drgerg/Pi-based-weather-station/Pics/BME280_mount-for-chimney.jpg

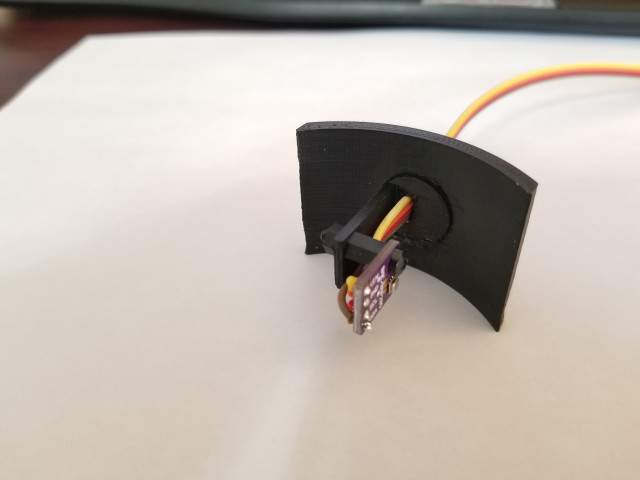
Pics/BME280_mount-for-chimney.jpg
