drgerg/Pi-based-weather-station/Pics/bottom-mount-hinge-perspective-view.jpg

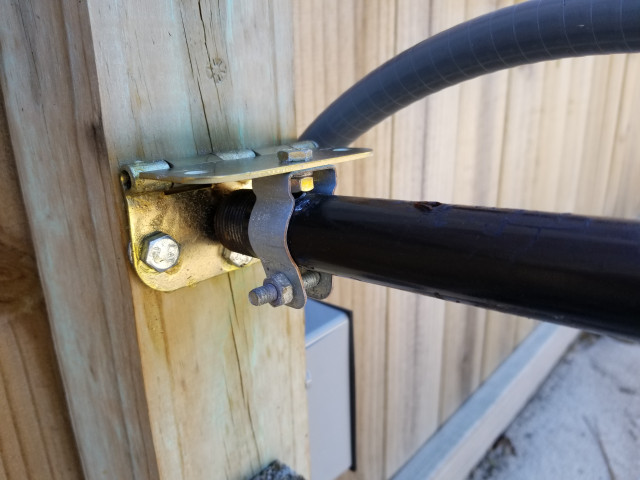
Pics/bottom-mount-hinge-perspective-view.jpg
