drgerg/Pi-based-weather-station/Pics/box-for-12VDC-arrestor-at-pole.jpg

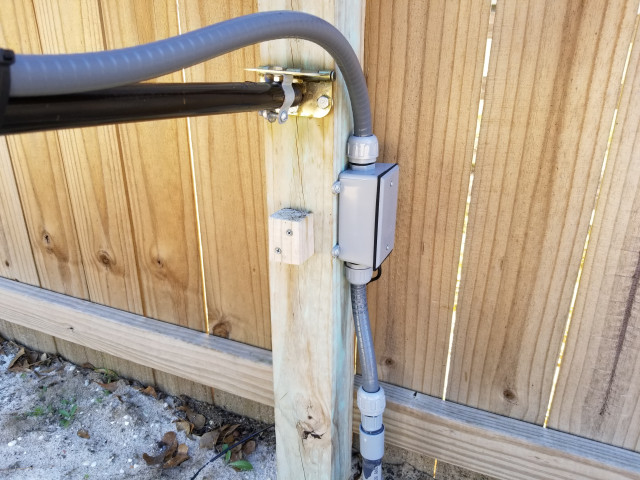
Pics/box-for-12VDC-arrestor-at-pole.jpg
