drgerg/Pi-based-weather-station/Pics/camera-module.jpg

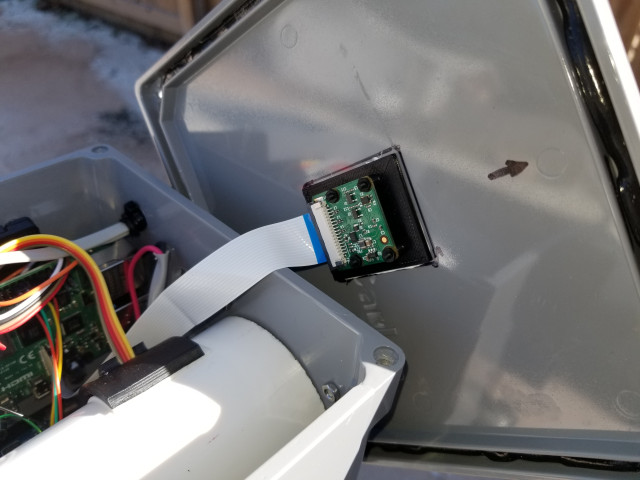
Pics/camera-module.jpg
