drgerg/Pi-based-weather-station/Pics/custom-10-pin-header.jpg

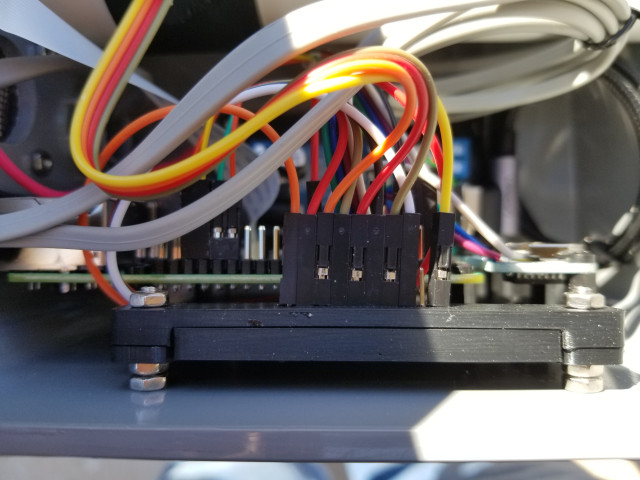
Pics/custom-10-pin-header.jpg
