drgerg/Pi-based-weather-station/Pics/DROK-buck-DC2DC-converter.jpg

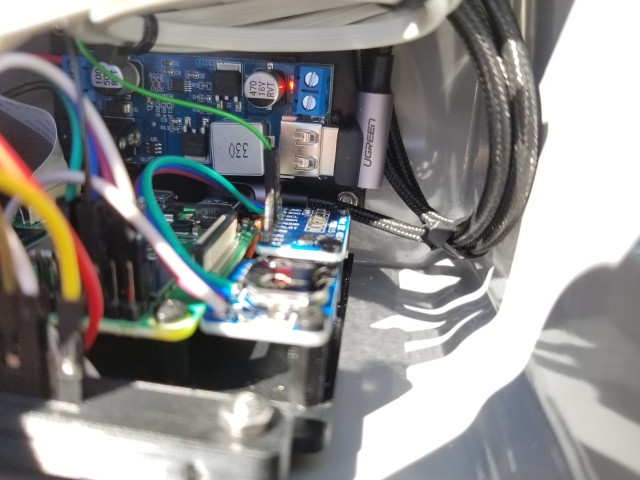
Pics/DROK-buck-DC2DC-converter.jpg
