drgerg/Pi-based-weather-station/Pics/Everything-guts-out-full-size.jpg

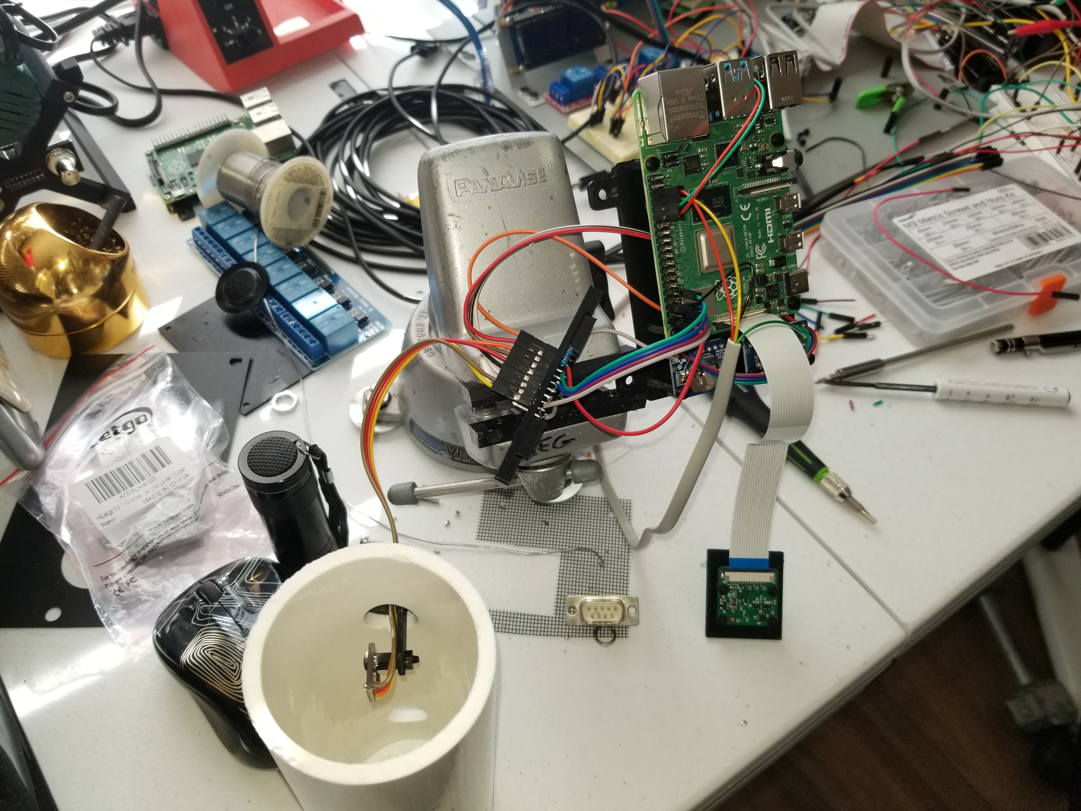
Pics/Everything-guts-out-full-size.jpg
