drgerg/Pi-based-weather-station/Pics/Inside-the-box.jpg

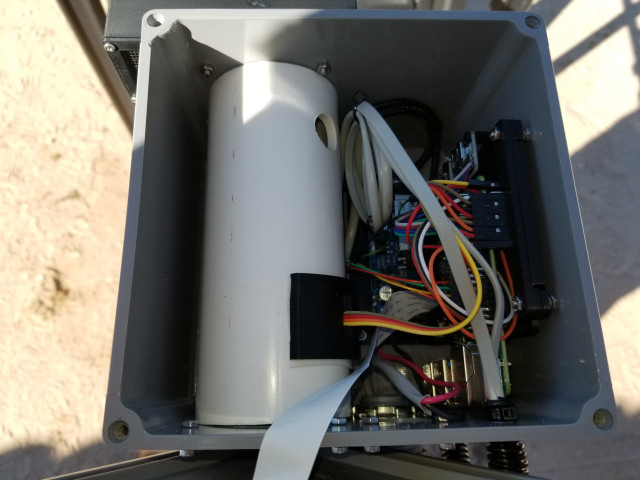
Pics/Inside-the-box.jpg
