drgerg/Pi-based-weather-station/Pics/module-mounting-nylon-standoffs.jpg

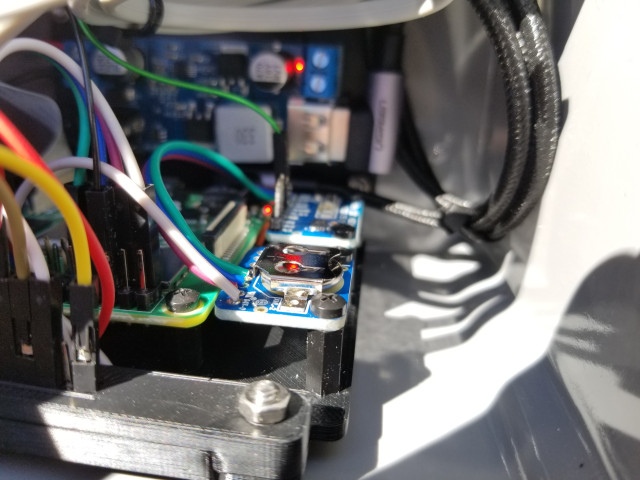
Pics/module-mounting-nylon-standoffs.jpg
