drgerg/Pi-based-weather-station/Pics/mother_main_screen.png

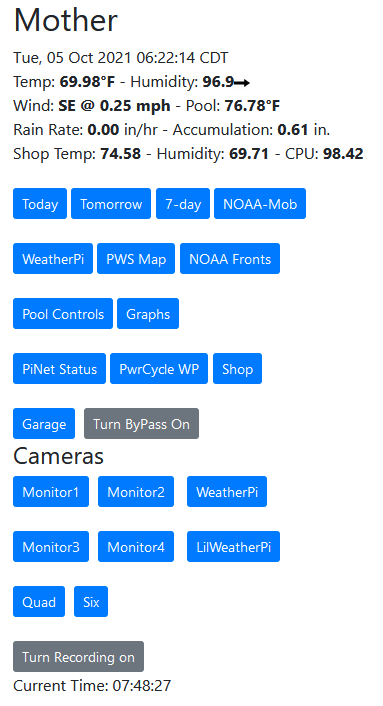
Pics/mother_main_screen.png
