drgerg/Pi-based-weather-station/Pics/outdata.outraw_table.jpg

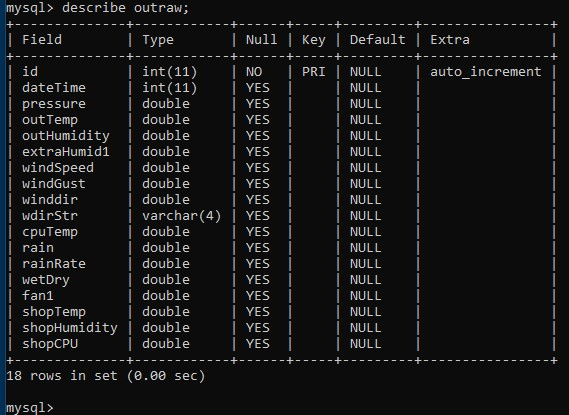
Pics/outdata.outraw_table.jpg
