drgerg/Pi-based-weather-station/Pics/Pi-mount-ADC-RTC.jpg

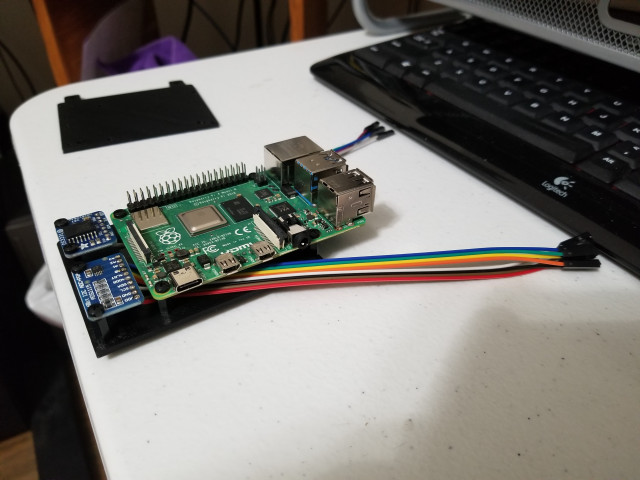
Pics/Pi-mount-ADC-RTC.jpg
