drgerg/Pi-based-weather-station/Pics/Screen_lookingUpChimney.jpg

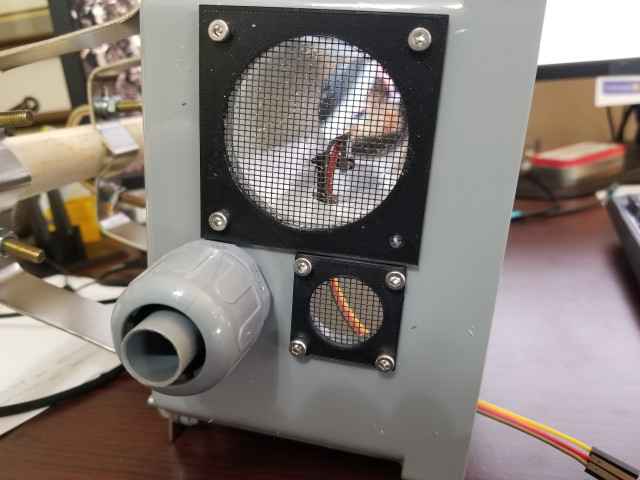
Pics/Screen_lookingUpChimney.jpg
