drgerg/Pi-based-weather-station/Pics/sensor-wires-enter-pipe.jpg

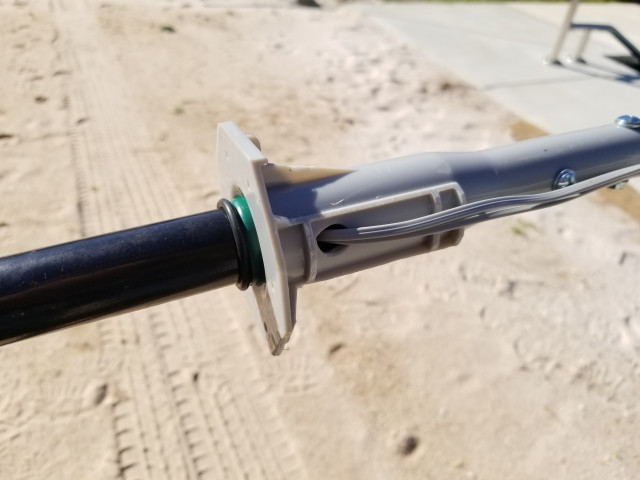
Pics/sensor-wires-enter-pipe.jpg
