drgerg/Pi-based-weather-station/Component_Docs/Power Parts/120VAC to 12VDC power supply.jpg

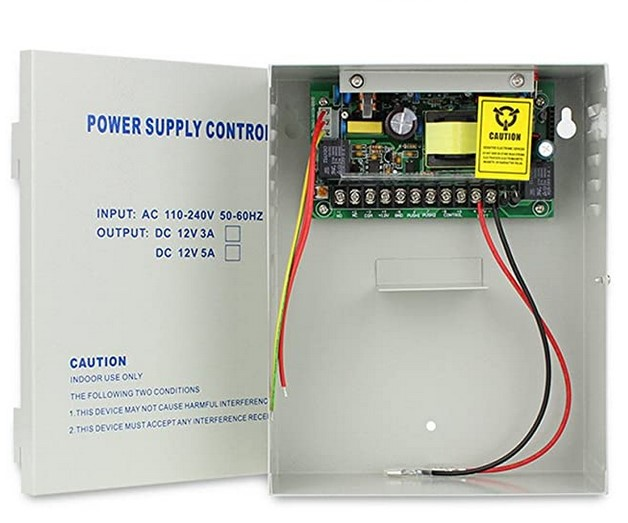
Component_Docs/Power Parts/120VAC to 12VDC power supply.jpg
