drgerg/Pi-based-weather-station/Component_Docs/Power Parts/DROK USB Buck Converter Voltage Regulator.png

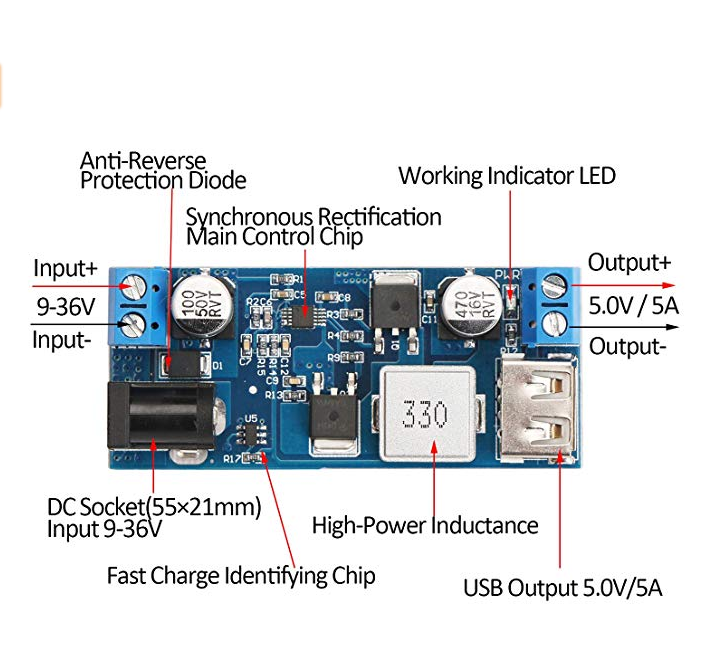
Component_Docs/Power Parts/DROK USB Buck Converter Voltage Regulator.png
