drgerg/Pi-based-weather-station/Component_Docs/Power Parts/LRS01-DC12V Lightning Arrestor.jpg

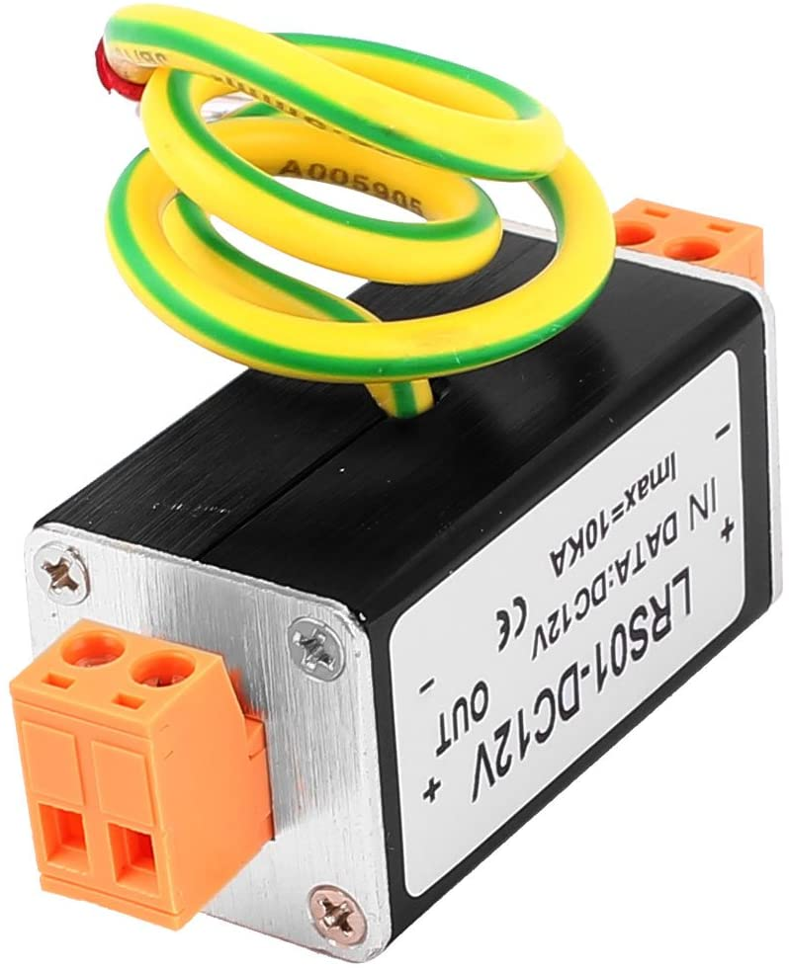
Component_Docs/Power Parts/LRS01-DC12V Lightning Arrestor.jpg
