drgerg/Pi-based-weather-station/Component_Docs/Power Parts/Weatherproof box for Power Supply.jpg

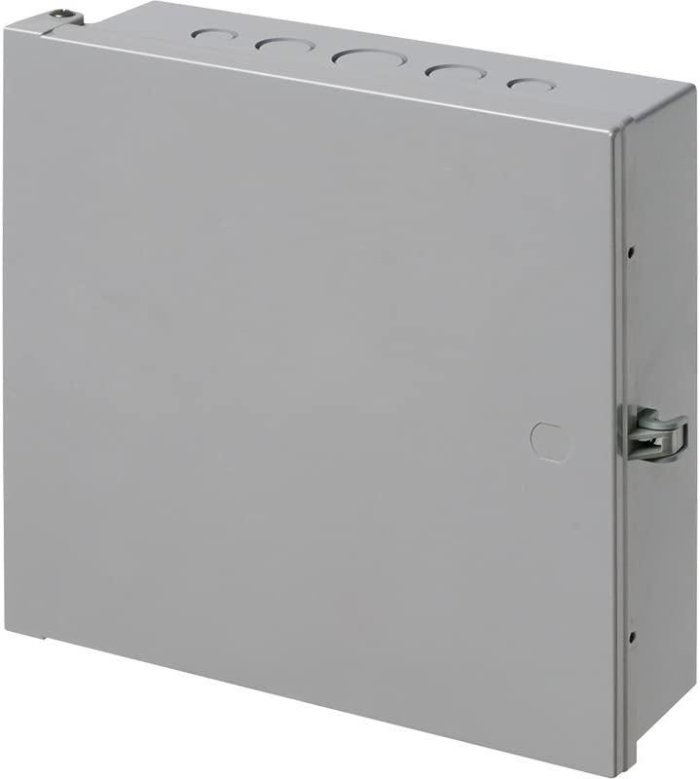
Component_Docs/Power Parts/Weatherproof box for Power Supply.jpg
