drgerg/Pi-based-weather-station/Pics/another-view-of-components.jpg

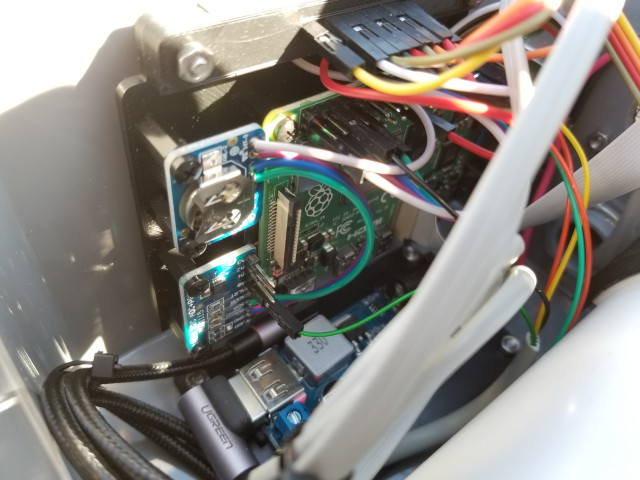
Pics/another-view-of-components.jpg
