drgerg/Pi-based-weather-station/Component_Docs/Fan_Ventilation_Custom/4-wireVariableSpeedFanWiringBeginningPoint.jpg

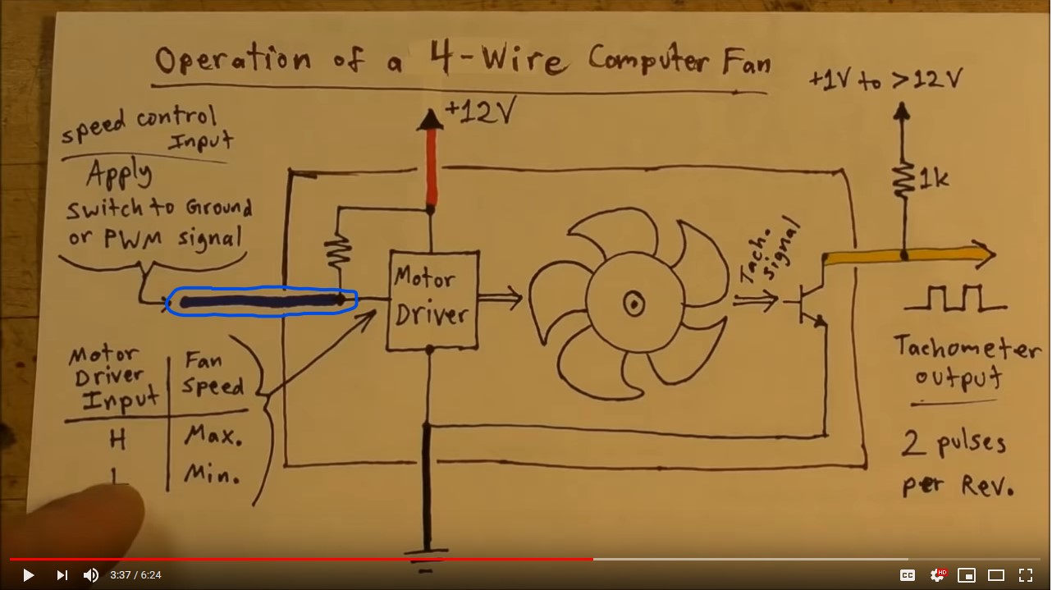
Component_Docs/Fan_Ventilation_Custom/4-wireVariableSpeedFanWiringBeginningPoint.jpg
