drgerg/Pi-based-weather-station/Component_Docs/Power Parts/Completed power supply installed.jpg

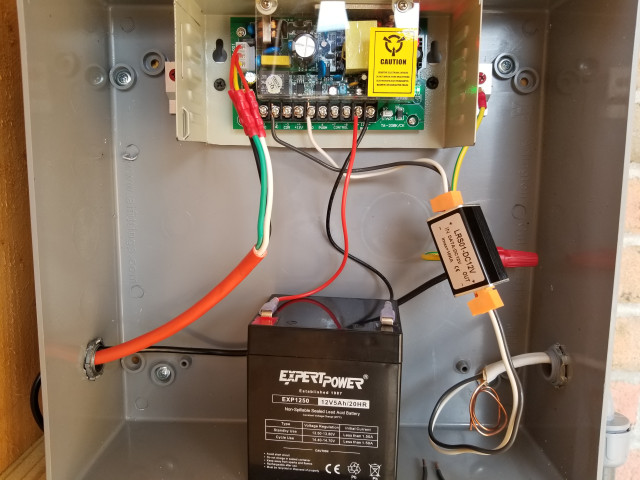
Component_Docs/Power Parts/Completed power supply installed.jpg
